Akrobate/retro-go-hardware/stl_files/screen-glass-piece.stl

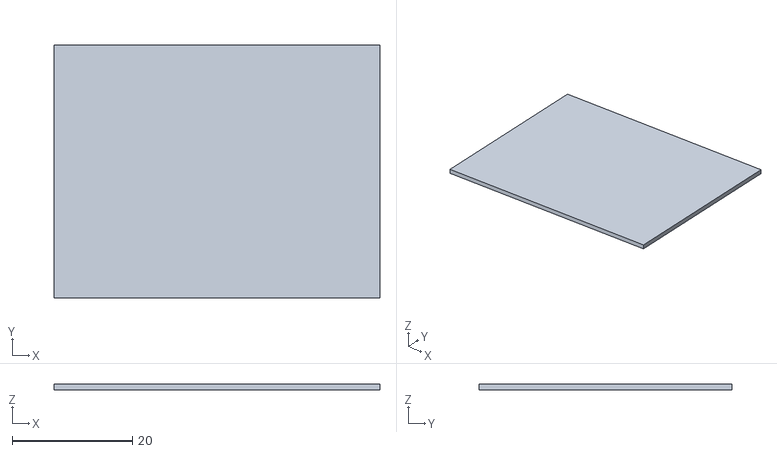
[picture p42: CAD file, 2024-03-25]
stl_files/screen-glass-piece.stl
54.2 x 42.1 x 1.00
