Akrobate/retro-go-hardware/stl_files/directional-cross-piece.stl

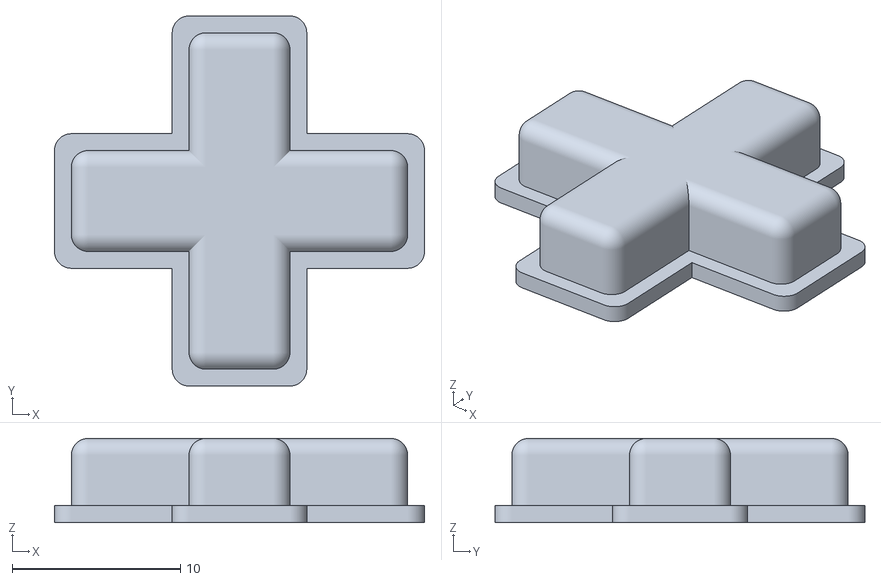
[picture p43: CAD file, 2024-02-10]
stl_files/directional-cross-piece.stl
22.0 x 22.0 x 5.00
