Akrobate/retro-go-hardware/stl_files/bolt-join-game-pad-piece.stl

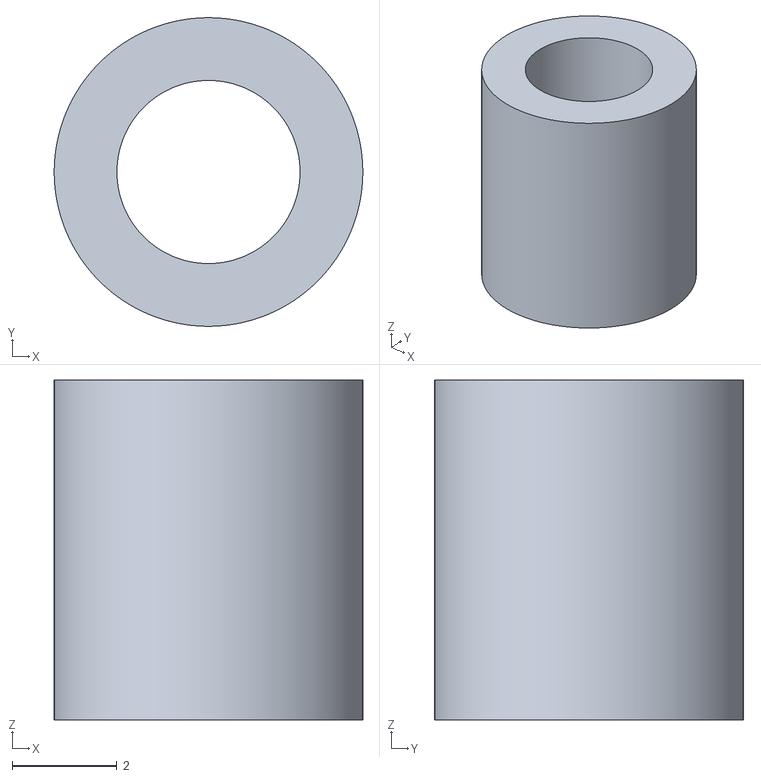
[picture p44: CAD file, 2024-03-28]
stl_files/bolt-join-game-pad-piece.stl
5.90 x 5.90 x 6.50
