Akrobate/retro-go-hardware/stl_files/bolt-join-mother-board-piece.stl

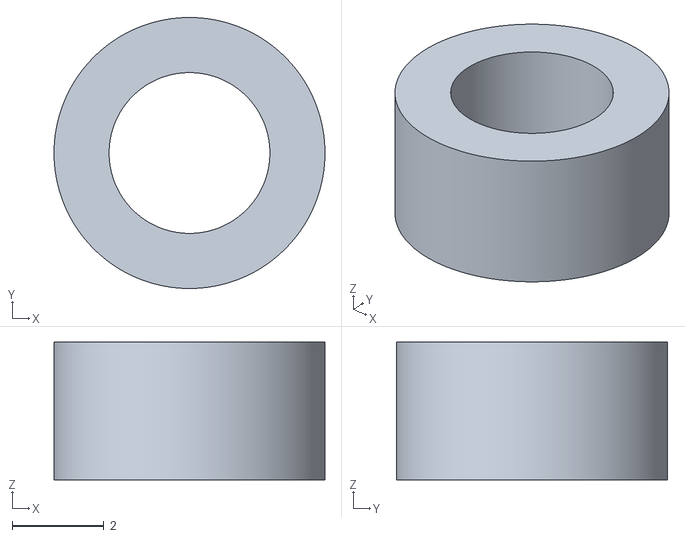
[picture p45: CAD file, 2024-03-28]
stl_files/bolt-join-mother-board-piece.stl
5.90 x 5.90 x 3.00
