Akrobate/retro-go-hardware/3D-models/assets/lcd-screen/configurations.scad

screen_asset_electronic_board_x_size = 72.25;
screen_asset_electronic_board_y_size = 43.25;
screen_asset_electronic_board_z_size = 1.25;

screen_asset_screen_external_x_size = 60.25;
screen_asset_screen_external_y_size = 42.7;
screen_asset_screen_external_z_size = 4 - 1.25;

screen_asset_throw_diameter = 3.1;

screen_asset_x_margin_throws_left = 1.6 + 1.55;
screen_asset_x_margin_throws_right = 1.5 + 1.55;
screen_asset_y_margin_throws_top = 1.55 + 1.55;
screen_asset_y_margin_throws_bottom = 1.4 + 1.55;
