Akrobate/retro-go-hardware/3D-models/assets/roundButton/configurations.scad

// A and B Buttons
round_button_1_diameter = 7.5;
round_button_1_z_size = 4;
round_button_1_support_diameter = 9.5;
round_button_1_support_z_size = 1;
round_button_1_fn = 80;
