Akrobate/retro-go-hardware/3D-models/assets/speaker-28mm/configurations.scad

speaker_asset_main_diameter = 28;
speaker_asset_main_z_size = 5.25;
speaker_asset_magnet_diameter = 16;
speaker_asset_magnet_z_size = 1.8;
speaker_asset_fn = 200;
