Akrobate/retro-go-hardware/3D-models/assets/usb-charger/configurations.scad

usb_charger_asset_electronic_card_x_size = 17.57;
usb_charger_asset_electronic_card_y_size = 27.85;
usb_charger_asset_electronic_card_z_size = 0.87;
usb_charger_asset_usb_port_x_size = 9;
usb_charger_asset_usb_port_y_size = 7.39;
usb_charger_asset_usb_port_z_size = 3.29;
usb_charger_asset_usb_round_radius = 1.5;
usb_charger_asset_draw_rounded_usb = true;
usb_charger_asset_usb_port_x_offset = 4.5;
usb_charger_asset_usb_port_y_offset = -1.36;
usb_charger_asset_fn = 20;
