Akrobate/retro-go-hardware/pieces/boldJoinPiece.scad

include <../configurations/global.scad>


module boltJoinPiece(
    internal_diameter = bolt_join_internal_diameter,
    external_diameter = bolt_join_external_diameter,
    height = bolt_join_height,
    _fn = bolt_join_fn
) {
    difference() {
        cylinder(d = external_diameter, h = height, center = true, $fn = _fn);

        cylinder(d = internal_diameter, h = height * 2, center = true, $fn = _fn);
    }
}

boltJoinPiece();
