Akrobate/retro-go-hardware/3D-models/pieces/directionalCrossPiece.scad

use <./subpieces/directionalCross.scad>
use <./subpieces/roundedPane.scad>

include <../configurations/global.scad>

/**
 * directionalCrossPiece
 * @name directionalCrossPiece
 * @description Cross button of gamepad
 * @type piece
 * @parent gamePadComponent
 */
module directionalCrossPiece(
    button_x_y_size = controller_cross_button_x_y_size,
    button_z_size = controller_cross_button_z_size,
    button_thickness = controller_cross_button_thickness,
    button_round_edges_radius = controller_cross_button_round_edges_radius,
    support_x_y_size = controller_cross_button_support_x_y_size,
    support_z_size = controller_cross_button_support_z_size,
    $fn = controller_cross_button_fn
) {
    union() {
        translate([0,0, (button_z_size + support_z_size) / 2]) {
            directionalCross(
                button_x_y_size,
                button_x_y_size,
                button_z_size + support_z_size,
                button_thickness,
                button_round_edges_radius,
                $fn = $fn
            );
        }
        
        translate([0,0, (support_z_size) / 2]) {
            roundedPane(
                [
                    support_x_y_size,
                    button_thickness + (support_x_y_size - button_x_y_size),
                    support_z_size
                ],
                button_round_edges_radius,
                button_round_edges_radius,
                center = true,
                $fn = $fn
            );

            roundedPane(
                [
                    button_thickness + (support_x_y_size - button_x_y_size),
                    support_x_y_size,
                    support_z_size
                ],
                button_round_edges_radius,
                button_round_edges_radius,
                center = true,
                $fn = $fn
            );

        }
    }
}

/**
 * @stl
 * @png
 * @colorscheme BeforeDawn
 * @view axes,scales
 */
directionalCrossPiece();
