Akrobate/retro-go-hardware/3D-models/assets/lcd-screen/screen.scad

include <./configurations.scad>

/**
 * screen
 * @name screen
 * @description Screen board
 * @type asset
 * @parent 
 */
module screen(
    electronic_board_x_size = screen_asset_electronic_board_x_size,
    electronic_board_y_size = screen_asset_electronic_board_y_size,
    electronic_board_z_size = screen_asset_electronic_board_z_size,
    
    screen_external_x_size = screen_asset_screen_external_x_size,
    screen_external_y_size = screen_asset_screen_external_y_size,
    screen_external_z_size = screen_asset_screen_external_z_size,
    
    throw_diameter = screen_asset_throw_diameter,
    
    x_margin_left = screen_asset_x_margin_throws_left,
    x_margin_right = screen_asset_x_margin_throws_right,
    y_margin_top = screen_asset_y_margin_throws_top,
    y_margin_bottom = screen_asset_y_margin_throws_bottom,    
    
    $fn = $fn
) {
    difference() {
        union() {
            color("RoyalBlue")
                cube(
                    [
                        electronic_board_x_size,
                        electronic_board_y_size,
                        electronic_board_z_size,
                    ]
                );
            translate([
                (electronic_board_x_size - screen_external_x_size) / 2,
                (electronic_board_y_size - screen_external_y_size) / 2,
                electronic_board_z_size
            ])
            color("white")
                cube(
                    [
                        screen_external_x_size,
                        screen_external_y_size,
                        screen_external_z_size,
                    ]
                );


            translate([
                (electronic_board_x_size - screen_external_x_size) / 2 + 1,
                (electronic_board_y_size - screen_external_y_size) / 2 + 1,
                electronic_board_z_size + 0.01
            ])
            color("black")
                cube(
                    [
                        screen_external_x_size - 1 - 6.5,
                        screen_external_y_size - 1 - 1,
                        screen_external_z_size,
                    ]
                );

            translate([0.85, 11.3, -8.25])
            cube([
                2.5,
                electronic_board_y_size - (11.3 * 2),
                8.25 + electronic_board_z_size + 1.6
            ]);
        }

        translate([x_margin_left, y_margin_bottom, - electronic_board_z_size / 2])
            cylinder(h = electronic_board_z_size * 2, d = throw_diameter, $fn = $fn);

        //
        translate([x_margin_left, electronic_board_y_size - y_margin_top, - electronic_board_z_size / 2])
            cylinder(h = electronic_board_z_size * 2, d = throw_diameter, $fn = $fn);

        // 
        translate([electronic_board_x_size - x_margin_right, electronic_board_y_size - y_margin_top, - electronic_board_z_size / 2])
            cylinder(h = electronic_board_z_size * 2, d = throw_diameter, $fn = $fn);

        translate([electronic_board_x_size - x_margin_right, y_margin_bottom, - electronic_board_z_size / 2])
            cylinder(h = electronic_board_z_size * 2, d = throw_diameter, $fn = $fn);

    }
}

screen($fn = 50);
