Akrobate/retro-go-hardware/3D-models/assets/on-off-button/on-off-button.scad

/**
 * onOffButton
 * @name onOffButton
 * @description Simple On Off button
 * @type asset
 * @parent 
 */
module onOffButton(
    $fn = 100
) {

    bottom_part_z_size = 6 + 12 + (6 / 2);
    bottom_part_diameter = 11.90; // M12 * 0.75

    support_z_size = 1.6;
    support_diameter_1 = 14;
    support_diameter_2 = 9 + 1;

    button_z_size = 3;
    button_diameter = 9;

    translate([0, 0, -bottom_part_z_size])
        cylinder(h=bottom_part_z_size, d=bottom_part_diameter, $fn = $fn);

    cylinder(
        h = support_z_size,
        d1 = support_diameter_1,
        d2 = support_diameter_2,
        $fn = $fn
    );

    cylinder(
        h = button_z_size,
        d = button_diameter,
        $fn = $fn
    );
}

onOffButton();
