Akrobate/retro-go-hardware/3D-models/assets/speaker-28mm/speaker-28mm.scad

include <configurations.scad>

/**
 * speaker28mm
 * @name speaker28mm
 * @description Simple design of 28mm diameter speaker
 * @type asset
 * @parent 
 */
module speaker28mm(
    speaker_asset_main_diameter = speaker_asset_main_diameter,
    speaker_asset_main_z_size = speaker_asset_main_z_size,
    speaker_asset_magnet_diameter = speaker_asset_magnet_diameter,
    speaker_asset_magnet_z_size = speaker_asset_magnet_z_size,
    speaker_asset_fn = speaker_asset_fn
) {
    color("DimGray")
        union() {
            translate([0, 0, -speaker_asset_main_z_size + speaker_asset_magnet_z_size])
                cylinder(
                    h = speaker_asset_main_z_size - speaker_asset_magnet_z_size,
                    d1 = speaker_asset_magnet_diameter,
                    d2 = speaker_asset_main_diameter,
                    $fn = speaker_asset_fn
                );
            
            translate([0, 0, -speaker_asset_main_z_size])
                cylinder(
                    h = speaker_asset_magnet_z_size,
                    d = speaker_asset_magnet_diameter,
                    $fn = speaker_asset_fn
                );
        }
}

speaker28mm();
