Akrobate/retro-go-hardware/3D-models/assets/usb-charger/usb-charger.scad

include <./configurations.scad>

/**
 * usbCharger
 * @name usbCharger
 * @description Usb Li-Ion charger board
 * @type asset
 * @parent 
 */
module usbCharger(
    electronic_card_x_size = usb_charger_asset_electronic_card_x_size,
    electronic_card_y_size = usb_charger_asset_electronic_card_y_size,
    electronic_card_z_size = usb_charger_asset_electronic_card_z_size,
    usb_port_x_size = usb_charger_asset_usb_port_x_size,
    usb_port_y_size = usb_charger_asset_usb_port_y_size,
    usb_port_z_size = usb_charger_asset_usb_port_z_size,
    usb_round_radius = usb_charger_asset_usb_round_radius,
    draw_rounded_usb = usb_charger_asset_draw_rounded_usb,
    usb_port_x_offset = usb_charger_asset_usb_port_x_offset,
    usb_port_y_offset = usb_charger_asset_usb_port_y_offset,
    _fn = usb_charger_asset_fn
) {
    color("RoyalBlue")
        cube([
            electronic_card_x_size,
            electronic_card_y_size,
            electronic_card_z_size
        ]);

    if (draw_rounded_usb) {

        usb_edges_coords = [
            [
                usb_round_radius,
                usb_round_radius
            ],
            [
                usb_port_x_size - usb_round_radius,
                usb_round_radius
            ],
            [
                usb_port_x_size - usb_round_radius,
                usb_port_z_size - usb_round_radius
            ],
            [
                usb_round_radius,
                usb_port_z_size - usb_round_radius
            ],
        ];

        color("DarkGray")
            translate([
                usb_port_x_offset,
                usb_port_y_offset,
                electronic_card_z_size
            ])
                hull() {
                    for (edge = usb_edges_coords) {
                        translate([edge[0], 0, edge[1]])
                            rotate([-90,0,0])
                                cylinder(h = usb_port_y_size, r = usb_round_radius, $fn = _fn);
                    }
                }
    } else {

        color("DarkGray")
            translate([
                usb_port_x_offset,
                usb_port_y_offset,
                electronic_card_z_size
            ])
                cube([
                    usb_port_x_size,
                    usb_port_y_size,
                    usb_port_z_size
                ]);
    }
}

usbCharger();
