Akrobate/retro-go-hardware/electronic/kicad/retro-go-hardware/retro-go-hardware.kicad_sch

## KiCad design electronic/kicad/retro-go-hardware/retro-go-hardware.kicad_sch (2024-04-23)

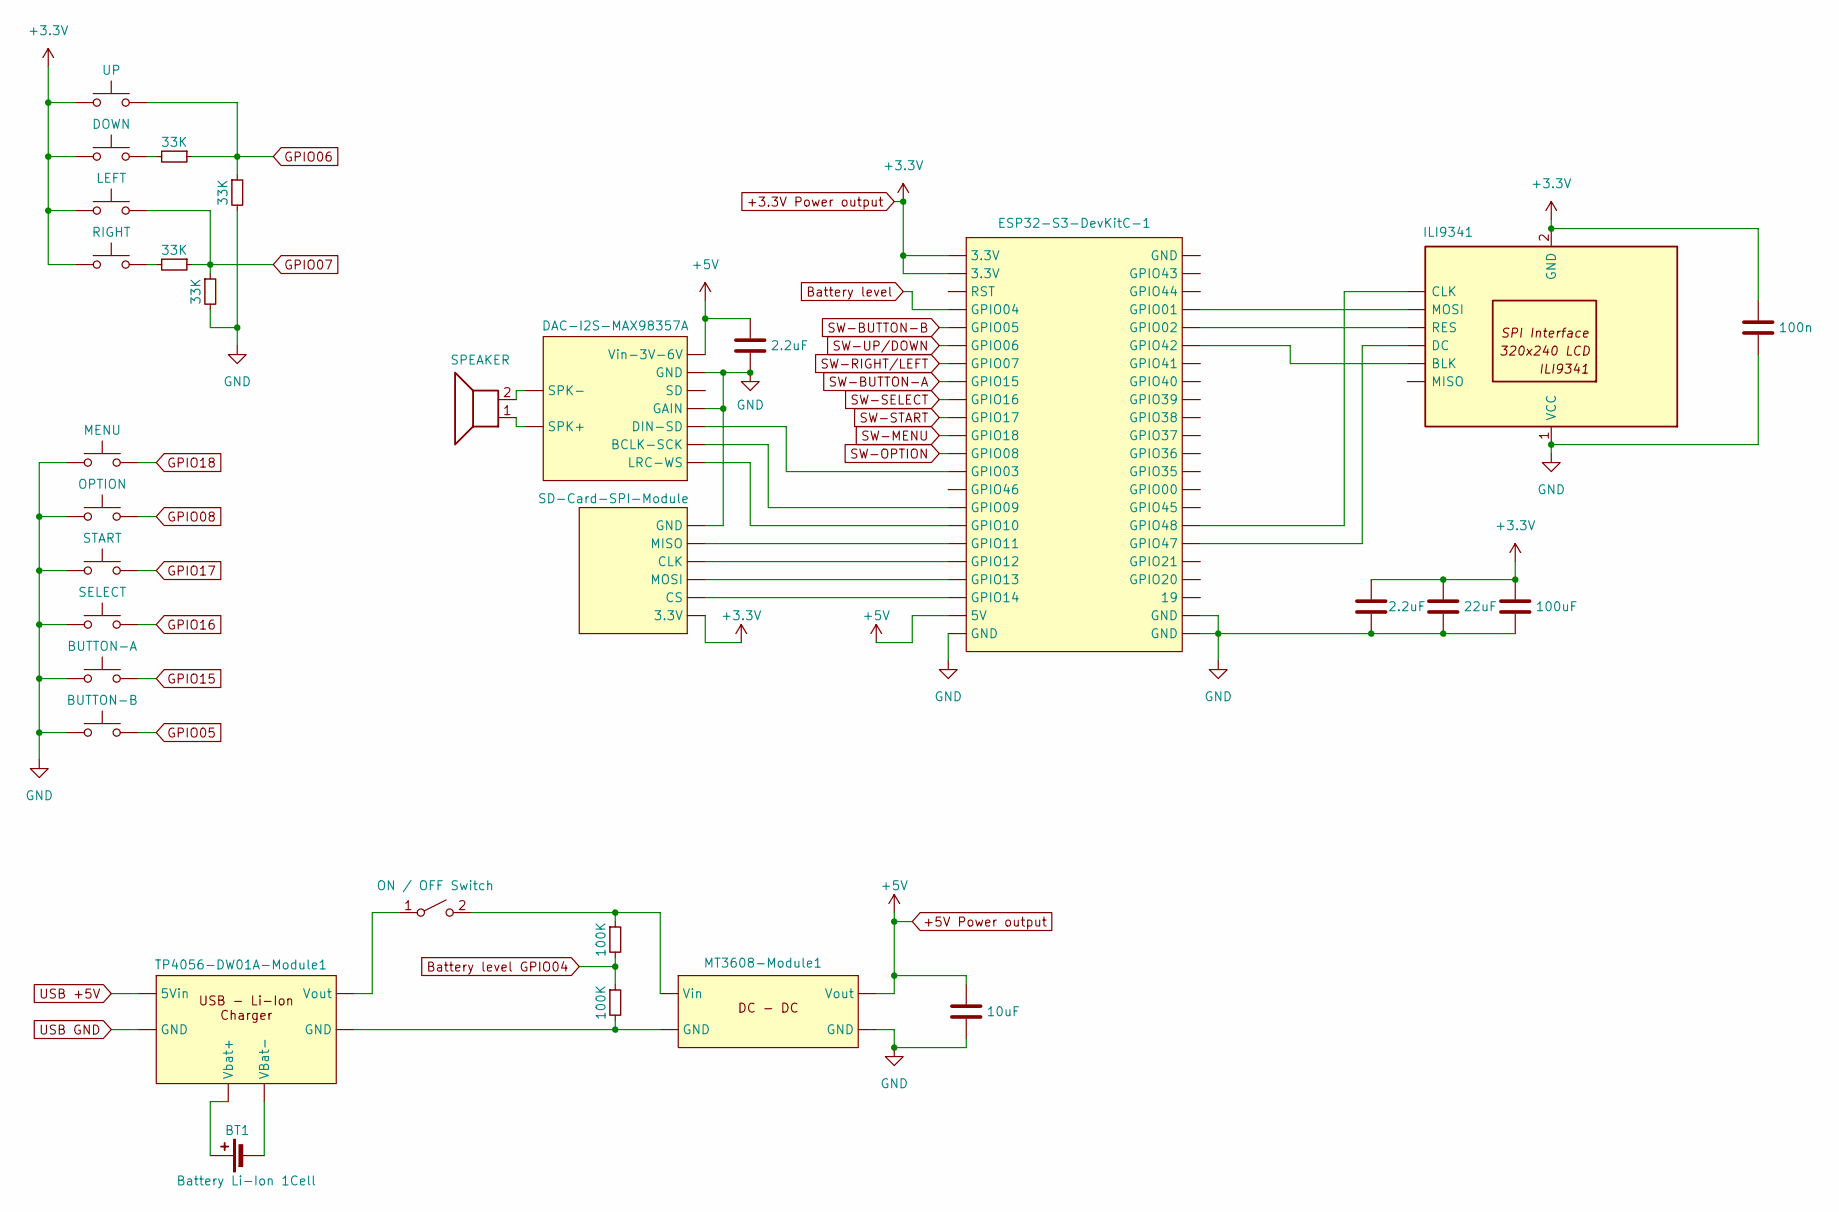
[picture p51: schematic retro-go-hardware.kicad_sch]

Parts:
2.2uF, 10uF, 22uF, 100n, 100uF: C
BT1: Battery Li-Ion 1Cell
BUTTON-A: (no value)
BUTTON-B: (no value)
DAC-I2S-MAX98357A: (no value)
DOWN: (no value)
ESP32-S3-DevKitC-1: (no value)
ILI9341: (no value)
LEFT: (no value)
MENU: (no value)
MT3608-Module1: (no value)
OPTION: (no value)
R1, R2, R3, R4: 33K
R5, R6: 100K
RIGHT: (no value)
SD-Card-SPI-Module: (no value)
SELECT: (no value)
SPEAKER: Speaker
START: (no value)
SW1: ON / OFF Switch
TP4056-DW01A-Module1: (no value)
UP: (no value)

Connections:
+3.3V: 2.2uF.1, 22uF.1, 100n.1, 100uF.1, DOWN.1, ESP32-S3-DevKitC-1., ILI9341.2 (GND), LEFT.1, RIGHT.1, SD-Card-SPI-Module., UP.1
+5V: 2.2uF.1, 10uF.1, DAC-I2S-MAX98357A., ESP32-S3-DevKitC-1., MT3608-Module1.
Battery level: ESP32-S3-DevKitC-1.
Battery level GPIO04: R5.1, R6.2
GND: 2.2uF.2, 10uF.2, 22uF.2, 100n.2, 100uF.2, BUTTON-A.1, BUTTON-B.1, DAC-I2S-MAX98357A., ESP32-S3-DevKitC-1., ILI9341.1 (VCC), MENU.1, MT3608-Module1., OPTION.1, R3.2, R4.2, SD-Card-SPI-Module., SELECT.1, START.1
GPIO05: BUTTON-B.2
GPIO06: R1.1, R3.1, UP.2
GPIO07: LEFT.2, R2.1, R4.1
GPIO08: OPTION.2
GPIO15: BUTTON-A.2
GPIO16: SELECT.2
GPIO17: START.2
GPIO18: MENU.2
unnamed: BT1.1 (+), TP4056-DW01A-Module1.
unnamed: BT1.2 (-), TP4056-DW01A-Module1.
unnamed: DAC-I2S-MAX98357A., ESP32-S3-DevKitC-1., SPEAKER.1, SPEAKER.2
unnamed: DOWN.2, R1.2
unnamed: ESP32-S3-DevKitC-1., ILI9341. (BLK), SD-Card-SPI-Module.
unnamed: MT3608-Module1., R5.2, R6.1, SW1.2 (B), TP4056-DW01A-Module1.
unnamed: R2.2, RIGHT.2
unnamed: SW1.1 (A), TP4056-DW01A-Module1.
SW-BUTTON-A: ESP32-S3-DevKitC-1.
SW-BUTTON-B: ESP32-S3-DevKitC-1.
SW-MENU: ESP32-S3-DevKitC-1.
SW-OPTION: ESP32-S3-DevKitC-1.
SW-RIGHT/LEFT: ESP32-S3-DevKitC-1.
SW-SELECT: ESP32-S3-DevKitC-1.
SW-START: ESP32-S3-DevKitC-1.
SW-UP/DOWN: ESP32-S3-DevKitC-1.
USB +5V: TP4056-DW01A-Module1.
USB GND: TP4056-DW01A-Module1.
